101zh/DOD/pictures/IMG_4681.jpeg

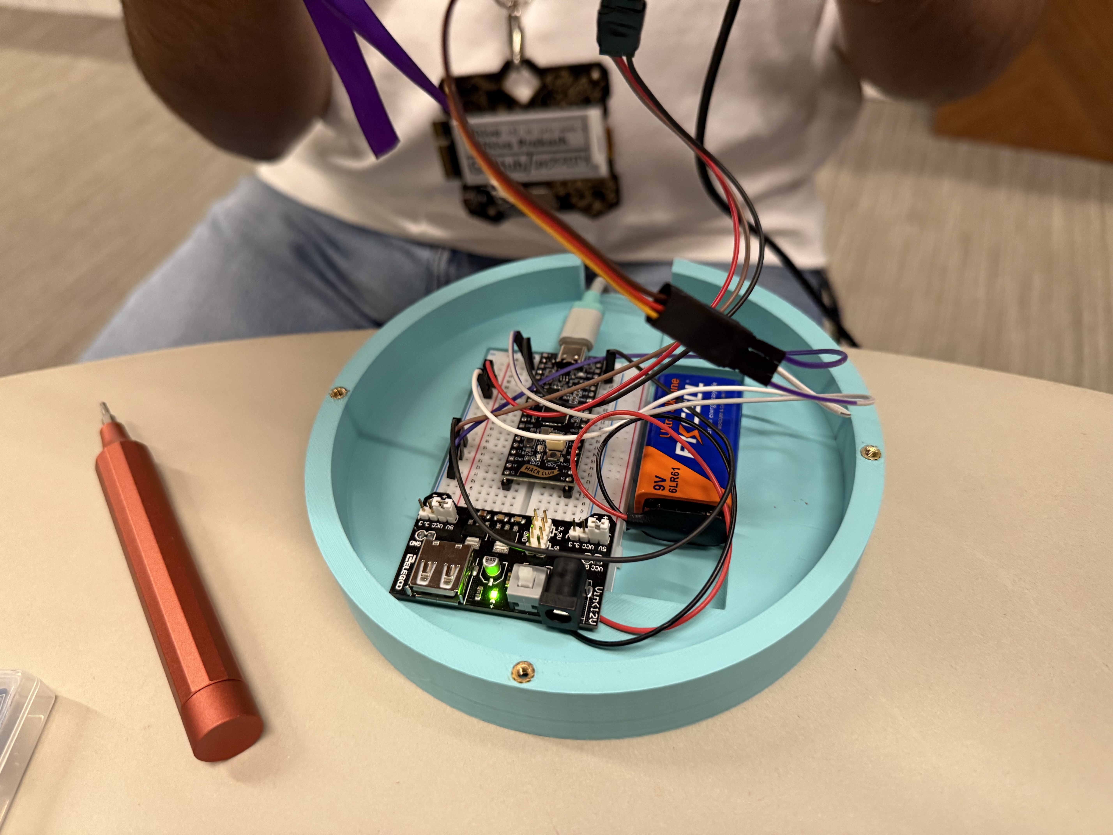
pictures/IMG_4681.jpeg
