101zh/DOD/pictures/IMG_4652.jpeg

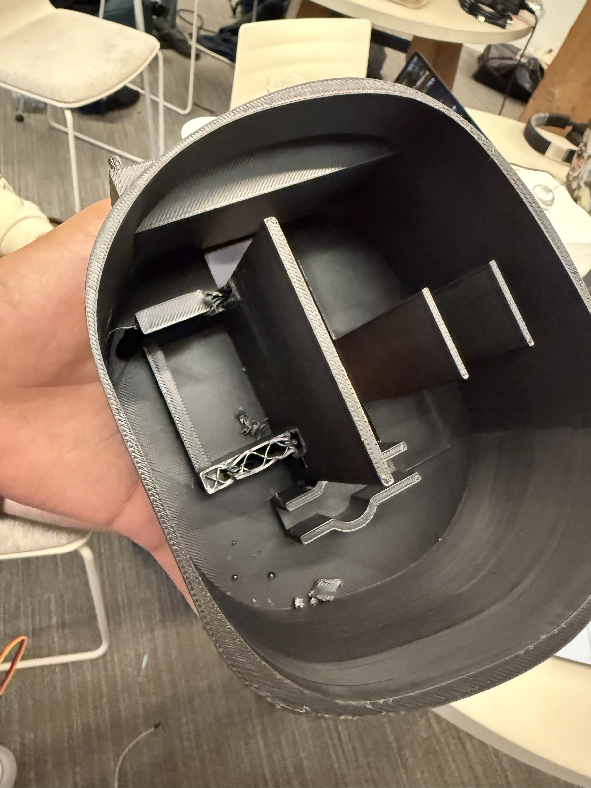
pictures/IMG_4652.jpeg
