101zh/DOD/pictures/IMG_4675.jpeg

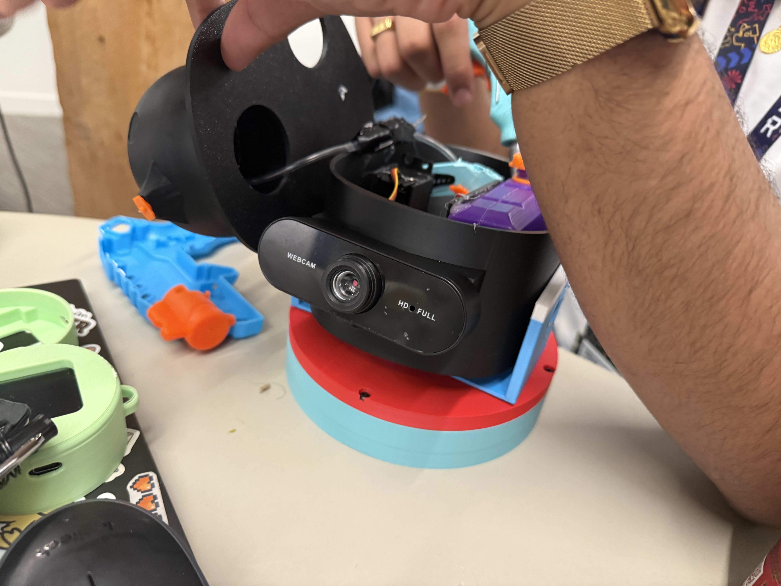
pictures/IMG_4675.jpeg
