101zh/DOD/pictures/IMG_4674.jpeg

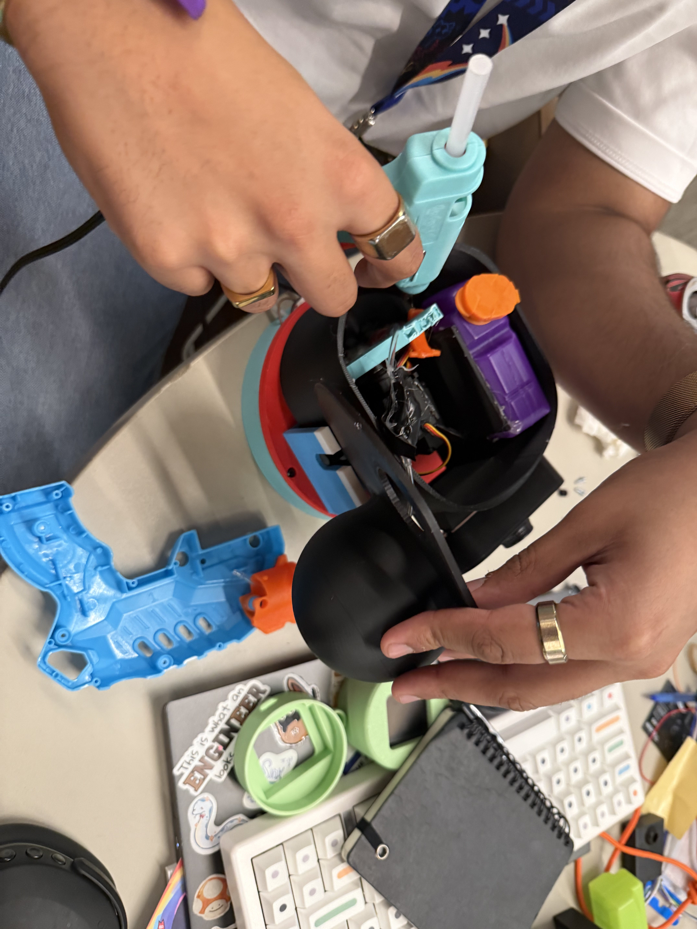
pictures/IMG_4674.jpeg
